sirbull/bitbot/docs/faces/01-neutral.png

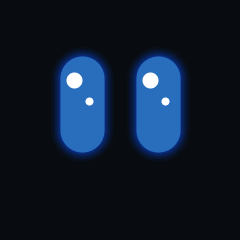
docs/faces/01-neutral.png
