sirbull/bitbot/docs/faces/02-happy.png

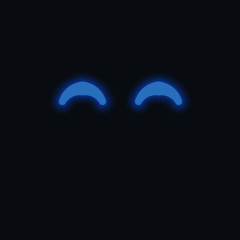
docs/faces/02-happy.png
