sirbull/bitbot/docs/faces/03-surprised.png

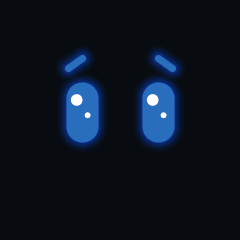
docs/faces/03-surprised.png
