sirbull/bitbot/docs/faces/10-winking.png

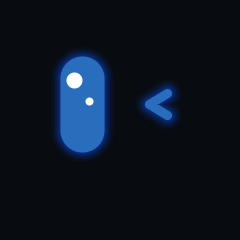
docs/faces/10-winking.png
